linvswin/mandjBeep/android/img/Screenshot_2016-06-06-07-36-31.png

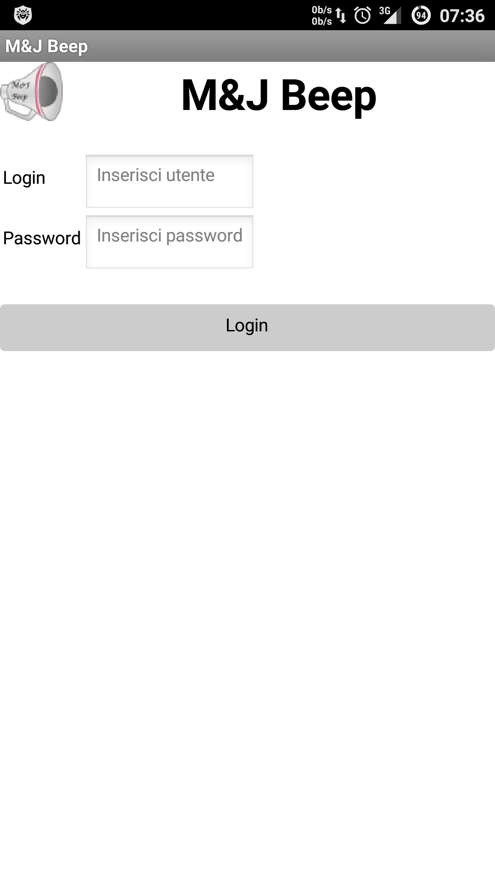
android/img/Screenshot_2016-06-06-07-36-31.png
