linvswin/mandjBeep/android/img/Screenshot_2016-06-06-07-37-08.png

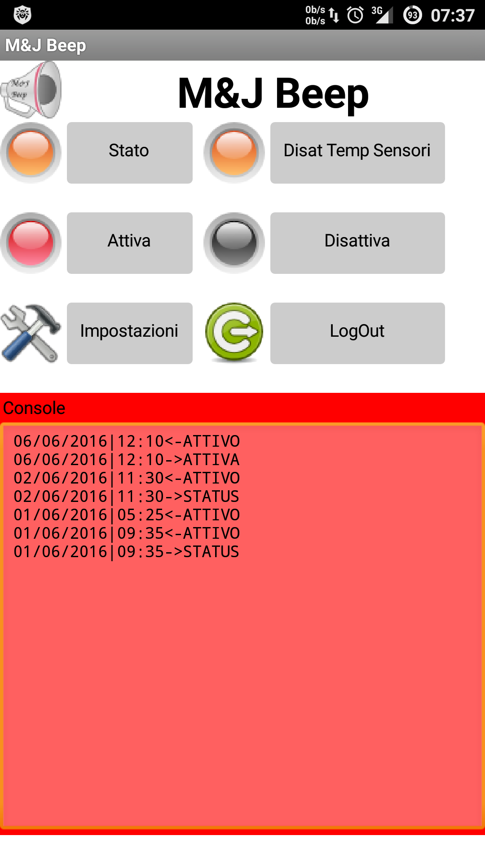
android/img/Screenshot_2016-06-06-07-37-08.png
