linvswin/mandjBeep/img/moduloCicalinoAntenna.jpg

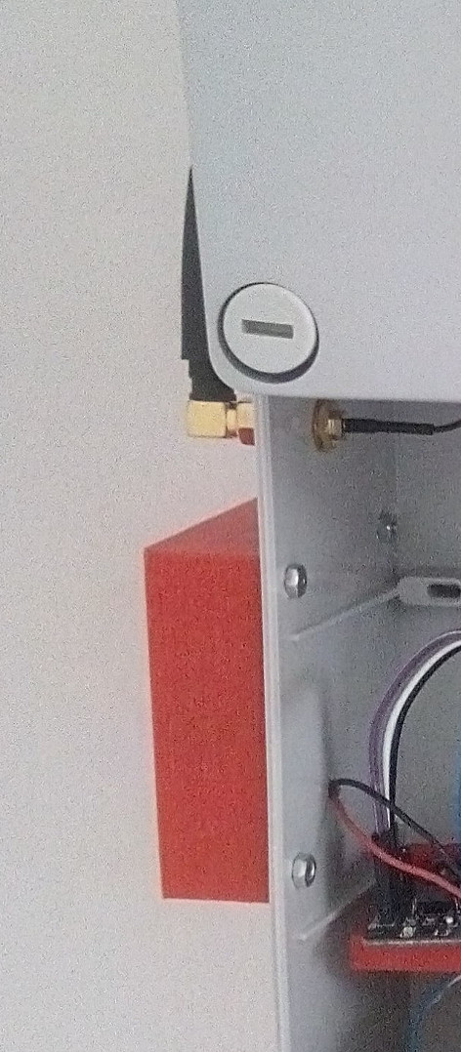
img/moduloCicalinoAntenna.jpg
