linvswin/mandjBeep/img/moduloCore.jpg

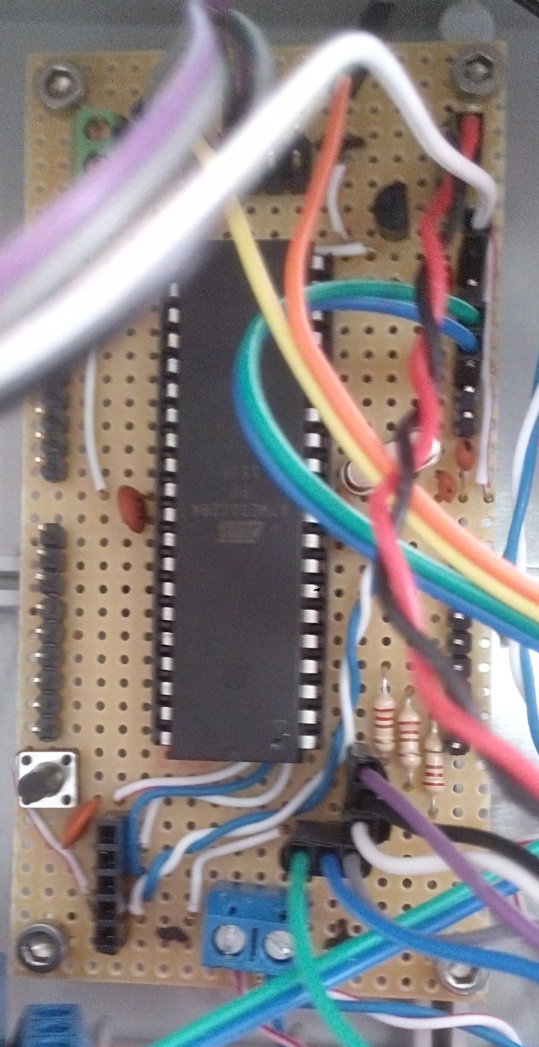
img/moduloCore.jpg
