linvswin/mandjBeep/img/moduloRelay.jpg

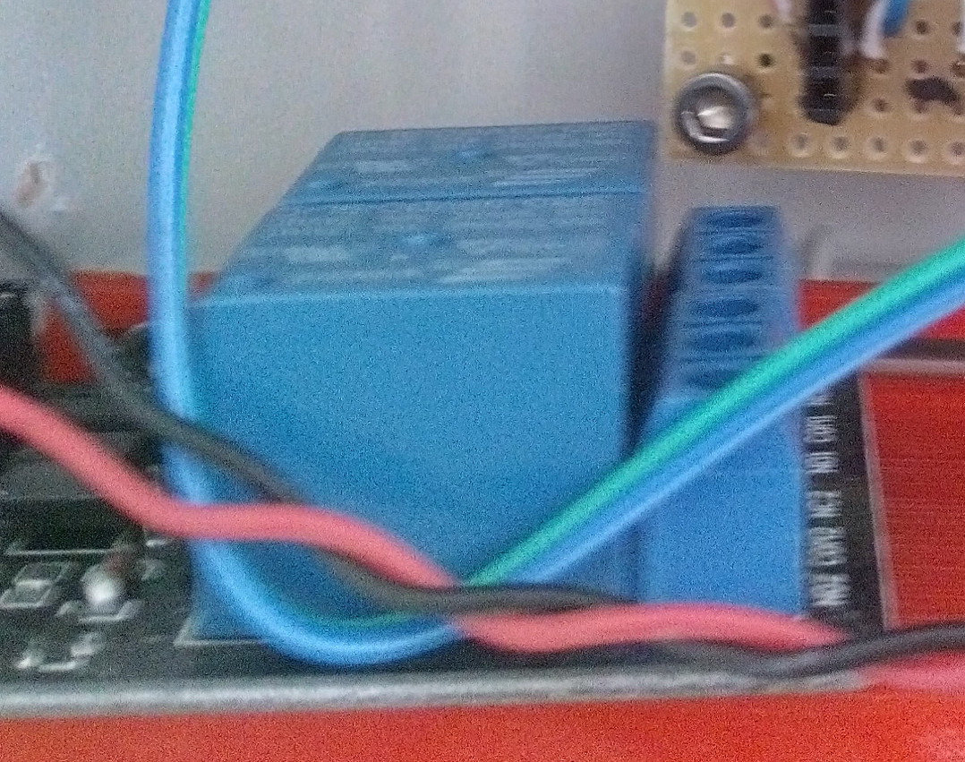
img/moduloRelay.jpg
