linvswin/mandjBeep/img/moduloSensori.jpg

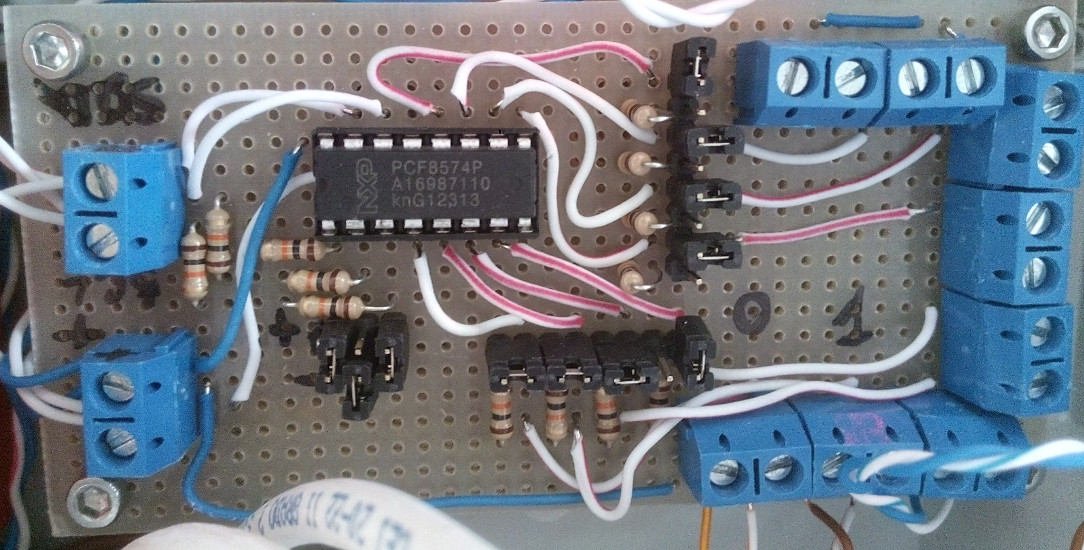
img/moduloSensori.jpg
