linvswin/mandjBeep/schema/mjBeep/baseBoard2.png

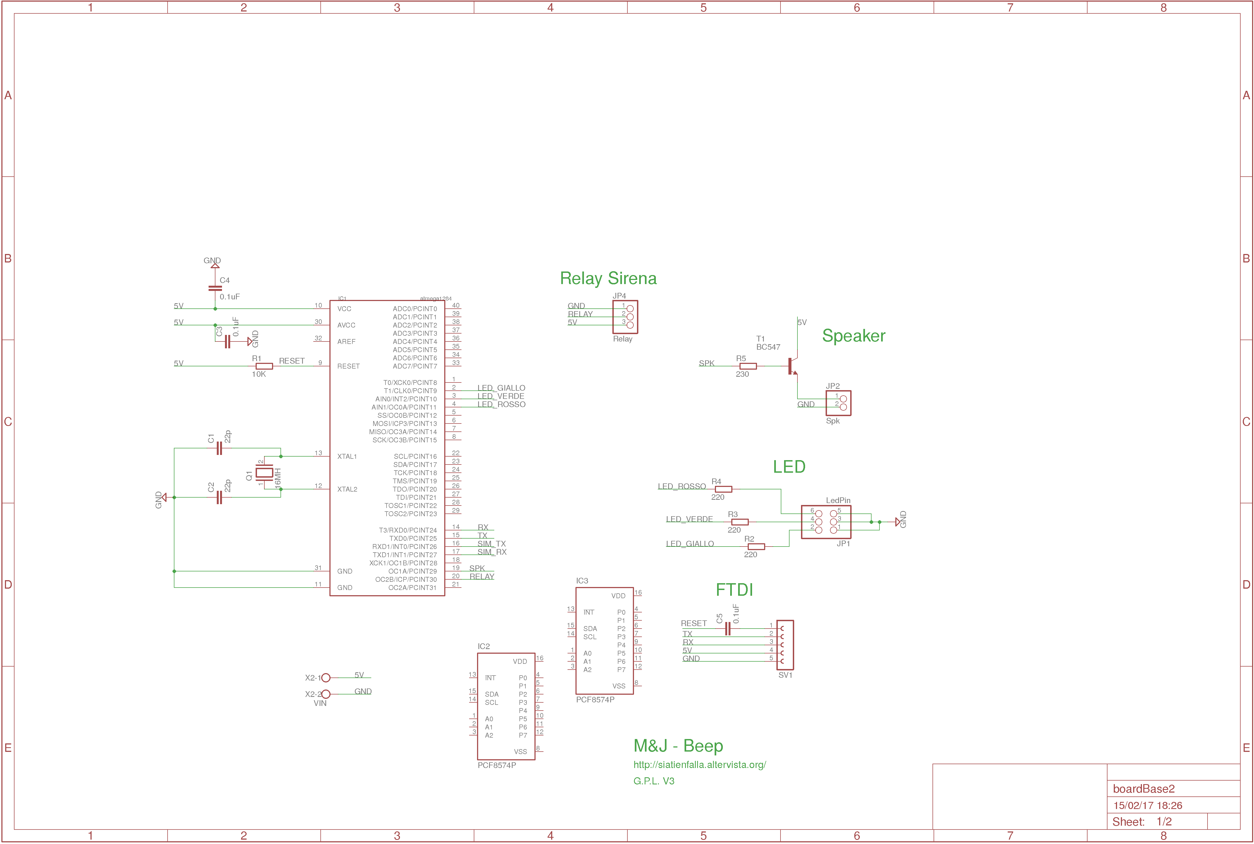
schema/mjBeep/baseBoard2.png
