linvswin/mandjBeep/def.h

/*
 * def.h
 *
 *  Created on: 23/feb/2016
 *      Author: peppe
 */

#ifndef DEF_H_
#define DEF_H_

void printDate();
void keypadEvent(KeypadEvent eKey);

void doAfterTimerT();
void doAfterRitActivate();
void doAfterRitardoTrigged();
void readGSMSlave();

bool setPulseWidth(long microseconds);
void doPrintRitAttivazione();
void timerDoLCDbacklight();

void inviaSMScomando(/*char *number_str,*/ char *message_str, char type);

#ifdef DEBUG_SETTINGS
void printSettings();
#endif

#endif /* DEF_H_ */
